DigiTorus86/ESP32Badge/hello-badge/esp32-badge-wav-play/audio_wav.h

/* D:\Projects\Assets\CodeMashBadge\alive8.wav (11/29/2019 5:37:46 PM)
   StartOffset: 00000000, EndOffset: 0000885F, Length: 00008860 
   Exported from Audacity as 8-bit 11025Hz mono PCM WAV file
   Exported from HxD Hex Editor as C code  (File -> Export -> C)
*/
   
const PROGMEM uint8_t audio_wav[34912] = {
  0x52, 0x49, 0x46, 0x46, 0x58, 0x88, 0x00, 0x00, 0x57, 0x41, 0x56, 0x45,
  0x66, 0x6D, 0x74, 0x20, 0x10, 0x00, 0x00, 0x00, 0x01, 0x00, 0x01, 0x00,
  0x11, 0x2B, 0x00, 0x00, 0x11, 0x2B, 0x00, 0x00, 0x01, 0x00, 0x08, 0x00,
  0x64, 0x61, 0x74, 0x61, 0x34, 0x88, 0x00, 0x00, 0x81, 0x80, 0x81, 0x7F,
  0x80, 0x7F, 0x7F, 0x80, 0x7F, 0x80, 0x80, 0x7F, 0x80, 0x7F, 0x80, 0x7F,
  0x80, 0x7F, 0x80, 0x7F, 0x80, 0x7F, 0x80, 0x7F, 0x80, 0x80, 0x7F, 0x80,
  0x7F, 0x80, 0x80, 0x7F, 0x80, 0x7F, 0x80, 0x80, 0x80, 0x80, 0x80, 0x7F,
  0x80, 0x80, 0x80, 0x81, 0x80, 0x7F, 0x80, 0x80, 0x7F, 0x80, 0x7F, 0x80,
  0x7F, 0x80, 0x7F, 0x80, 0x7F, 0x80, 0x7F, 0x7F, 0x80, 0x7F, 0x80, 0x7F,
  0x7F, 0x80, 0x7F, 0x80, 0x7F, 0x80, 0x7F, 0x80, 0x7F, 0x80, 0x80, 0x80,
  0x7F, 0x80, 0x7F, 0x80, 0x80, 0x7F, 0x80, 0x80, 0x7F, 0x80, 0x7F, 0x80,
  0x7F, 0x80, 0x7F, 0x80, 0x7F, 0x80, 0x80, 0x7F, 0x80, 0x7F, 0x80, 0x80,
  0x80, 0x80, 0x7F, 0x80, 0x80, 0x80, 0x80, 0x7F, 0x80, 0x7F, 0x80, 0x80,
  0x81, 0x81, 0x80, 0x81, 0x80, 0x81, 0x80, 0x80, 0x80, 0x80, 0x7F, 0x80,
  0x7F, 0x81, 0x80, 0x80, 0x80, 0x7F, 0x80, 0x7F, 0x80, 0x7F, 0x80, 0x80,
  0x81, 0x7F, 0x80, 0x80, 0x81, 0x80, 0x81, 0x7F, 0x80, 0x7F, 0x81, 0x81,
  0x80, 0x80, 0x80, 0x80, 0x81, 0x80, 0x80, 0x7F, 0x80, 0x80, 0x82, 0x80,
  0x7F, 0x81, 0x81, 0x81, 0x7F, 0x80, 0x7F, 0x80, 0x7F, 0x80, 0x7F, 0x80,
  0x7F, 0x80, 0x80, 0x80, 0x81, 0x80, 0x81, 0x80, 0x81, 0x80, 0x81, 0x81,
  0x80, 0x81, 0x80, 0x80, 0x80, 0x7F, 0x80, 0x7F, 0x80, 0x80, 0x7F, 0x80,
  0x7F, 0x80, 0x7F, 0x80, 0x81, 0x81, 0x80, 0x80, 0x81, 0x82, 0x82, 0x80,
  0x7F, 0x81, 0x81, 0x81, 0x7E, 0x7E, 0x7F, 0x80, 0x80, 0x7E, 0x7F, 0x7F,
  0x7F, 0x80, 0x80, 0x80, 0x81, 0x80, 0x81, 0x81, 0x80, 0x81, 0x80, 0x80,
  0x80, 0x80, 0x81, 0x7F, 0x7F, 0x7F, 0x7E, 0x80, 0x7F, 0x7E, 0x7F, 0x7E,
  0x80, 0x80, 0x81, 0x80, 0x81, 0x80, 0x81, 0x82, 0x82, 0x83, 0x81, 0x80,
  0x81, 0x81, 0x81, 0x80, 0x7E, 0x7F, 0x7E, 0x7F, 0x7F, 0x7E, 0x7F, 0x7F,
  0x80, 0x80, 0x81, 0x80, 0x81, 0x80, 0x82, 0x81, 0x82, 0x81, 0x81, 0x80,
  0x81, 0x81, 0x7F, 0x7F, 0x7F, 0x7E, 0x7F, 0x7F, 0x7F, 0x7E, 0x7F, 0x7F,
  0x80, 0x81, 0x80, 0x81, 0x81, 0x82, 0x81, 0x82, 0x80, 0x80, 0x7F, 0x81,
  0x82, 0x85, 0x84, 0x7E, 0x7B, 0x7E, 0x82, 0x84, 0x7D, 0x79, 0x78, 0x7E,
  0x82, 0x84, 0x7F, 0x7D, 0x7F, 0x83, 0x85, 0x86, 0x83, 0x81, 0x80, 0x81,
  0x85, 0x84, 0x82, 0x7D, 0x7D, 0x7E, 0x81, 0x80, 0x7D, 0x7A, 0x7B, 0x7E,
  0x81, 0x80, 0x7E, 0x7F, 0x80, 0x83, 0x82, 0x83, 0x82, 0x82, 0x82, 0x81,
  0x82, 0x7F, 0x7E, 0x7E, 0x7F, 0x84, 0x84, 0x7E, 0x7B, 0x7C, 0x81, 0x83,
  0x82, 0x7E, 0x7C, 0x7F, 0x83, 0x83, 0x82, 0x80, 0x7E, 0x81, 0x82, 0x84,
  0x81, 0x80, 0x7E, 0x80, 0x82, 0x82, 0x81, 0x7F, 0x7E, 0x7F, 0x80, 0x81,
  0x7F, 0x7F, 0x7F, 0x7E, 0x7E, 0x80, 0x7F, 0x80, 0x7E, 0x7E, 0x80, 0x80,
  0x81, 0x80, 0x80, 0x80, 0x80, 0x7F, 0x7F, 0x80, 0x88, 0x8B, 0x82, 0x78,
  0x79, 0x80, 0x87, 0x80, 0x77, 0x74, 0x7A, 0x85, 0x84, 0x80, 0x7C, 0x7F,
  0x83, 0x88, 0x87, 0x85, 0x81, 0x7F, 0x82, 0x84, 0x86, 0x82, 0x7D, 0x79,
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
};
