DigiTorus86/ESP32Badge/esp32-badge-gravitack/TickWav.h

/* D:\Projects\Assets\CodeMashBadge\tickGx8.wav (9/9/2019 5:25:52 PM)
   StartOffset: 00000000, EndOffset: 000005E5, Length: 000005E6 */

unsigned char tick_wav[1510] = {
  0x52, 0x49, 0x46, 0x46, 0xDE, 0x05, 0x00, 0x00, 0x57, 0x41, 0x56, 0x45,
  0x66, 0x6D, 0x74, 0x20, 0x10, 0x00, 0x00, 0x00, 0x01, 0x00, 0x01, 0x00,
  0x22, 0x56, 0x00, 0x00, 0x22, 0x56, 0x00, 0x00, 0x01, 0x00, 0x08, 0x00,
  0x64, 0x61, 0x74, 0x61, 0xBA, 0x05, 0x00, 0x00, 0x7E, 0x7F, 0x82, 0x82,
  0x7E, 0x7E, 0x82, 0x83, 0x7E, 0x7B, 0x80, 0x83, 0x7D, 0x78, 0x8B, 0xB5,
  0xDF, 0xF7, 0xFF, 0xF8, 0xCE, 0x80, 0x30, 0x05, 0x00, 0x00, 0x01, 0x27,
  0x7A, 0xCF, 0xFC, 0xFF, 0xFD, 0xE6, 0xA9, 0x52, 0x13, 0x00, 0x00, 0x00,
  0x15, 0x58, 0xB0, 0xEC, 0xFF, 0xFF, 0xF5, 0xC6, 0x74, 0x29, 0x06, 0x01,
  0x00, 0x0C, 0x41, 0x94, 0xDA, 0xF9, 0xFF, 0xFA, 0xDA, 0x97, 0x48, 0x15,
  0x03, 0x00, 0x06, 0x2C, 0x73, 0xBD, 0xEC, 0xFF, 0xFF, 0xE9, 0xB2, 0x68,
  0x2B, 0x0B, 0x00, 0x02, 0x1C, 0x57, 0xA0, 0xDA, 0xF8, 0xFF, 0xF2, 0xC9,
  0x89, 0x47, 0x19, 0x04, 0x01, 0x14, 0x41, 0x83, 0xC2, 0xEC, 0xFD, 0xF8,
  0xD9, 0xA2, 0x62, 0x2D, 0x0E, 0x04, 0x0E, 0x30, 0x69, 0xA9, 0xDB, 0xF6,
  0xF9, 0xE5, 0xB9, 0x7E, 0x44, 0x1B, 0x09, 0x0B, 0x23, 0x52, 0x8E, 0xC6,
  0xEB, 0xF8, 0xED, 0xCB, 0x97, 0x5E, 0x2F, 0x12, 0x0B, 0x1B, 0x40, 0x76,
  0xAD, 0xDA, 0xF1, 0xF1, 0xD9, 0xAD, 0x77, 0x45, 0x20, 0x10, 0x17, 0x33,
  0x61, 0x96, 0xC6, 0xE7, 0xF1, 0xE2, 0xBE, 0x8E, 0x5C, 0x33, 0x1B, 0x17,
  0x29, 0x4E, 0x7F, 0xB1, 0xD7, 0xEA, 0xE6, 0xCD, 0xA3, 0x73, 0x46, 0x27,
  0x1B, 0x24, 0x40, 0x6A, 0x9A, 0xC5, 0xE0, 0xE6, 0xD6, 0xB4, 0x87, 0x5A,
  0x37, 0x23, 0x23, 0x36, 0x59, 0x86, 0xB1, 0xD2, 0xE0, 0xDA, 0xC1, 0x9A,
  0x6F, 0x48, 0x2E, 0x25, 0x30, 0x4B, 0x73, 0x9D, 0xC2, 0xD9, 0xDC, 0xCB,
  0xAA, 0x82, 0x5A, 0x3B, 0x2B, 0x2D, 0x41, 0x62, 0x8A, 0xB1, 0xCC, 0xD8,
  0xD0, 0xB8, 0x94, 0x6C, 0x4A, 0x34, 0x2E, 0x3A, 0x54, 0x78, 0x9F, 0xBF,
  0xD1, 0xD1, 0xC0, 0xA2, 0x7E, 0x5B, 0x40, 0x33, 0x36, 0x4A, 0x69, 0x8D,
  0xAF, 0xC7, 0xCF, 0xC7, 0xAF, 0x8F, 0x6B, 0x4D, 0x3A, 0x36, 0x43, 0x5C,
  0x7D, 0x9F, 0xBB, 0xCA, 0xC9, 0xB9, 0x9D, 0x7B, 0x5C, 0x44, 0x3A, 0x3E,
  0x51, 0x6D, 0x8E, 0xAD, 0xC1, 0xC7, 0xBE, 0xA8, 0x8A, 0x6B, 0x50, 0x40,
  0x3E, 0x4A, 0x61, 0x7F, 0x9E, 0xB6, 0xC3, 0xC1, 0xB2, 0x98, 0x7A, 0x5E,
  0x49, 0x41, 0x46, 0x56, 0x70, 0x8E, 0xA9, 0xBB, 0xC0, 0xB7, 0xA3, 0x88,
  0x6C, 0x54, 0x46, 0x45, 0x4F, 0x65, 0x80, 0x9B, 0xB1, 0xBC, 0xBA, 0xAD,
  0x96, 0x7A, 0x61, 0x4F, 0x47, 0x4B, 0x5A, 0x72, 0x8D, 0xA5, 0xB5, 0xBA,
  0xB2, 0xA1, 0x88, 0x6F, 0x59, 0x4C, 0x4A, 0x53, 0x66, 0x7E, 0x97, 0xAB,
  0xB5, 0xB5, 0xA9, 0x95, 0x7D, 0x66, 0x54, 0x4C, 0x4F, 0x5C, 0x71, 0x89,
  0x9F, 0xAE, 0xB4, 0xAE, 0xA0, 0x8B, 0x74, 0x60, 0x52, 0x4F, 0x55, 0x65,
  0x7A, 0x90, 0xA3, 0xAF, 0xB1, 0xA9, 0x98, 0x83, 0x6D, 0x5C, 0x52, 0x52,
  0x5C, 0x6C, 0x81, 0x95, 0xA6, 0xAE, 0xAD, 0xA2, 0x91, 0x7C, 0x69, 0x5A,
  0x54, 0x56, 0x60, 0x71, 0x85, 0x98, 0xA6, 0xAC, 0xA9, 0x9E, 0x8D, 0x79,
  0x67, 0x5B, 0x56, 0x59, 0x63, 0x74, 0x87, 0x98, 0xA5, 0xAA, 0xA6, 0x9C,
  0x8C, 0x7A, 0x69, 0x5D, 0x57, 0x5A, 0x64, 0x73, 0x85, 0x95, 0xA2, 0xA7,
  0xA5, 0x9C, 0x8E, 0x7D, 0x6D, 0x61, 0x5A, 0x5B, 0x62, 0x6F, 0x7F, 0x8F,
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
};
