DigiTorus86/ESP32Badge/esp32-badge-tombstone/Audio.h

/*
 * Audio and sound
 */


//Fifth Octave Note Frequencies
 
#define C5 523 // C note frequency
#define Cs5 554 // C sharp note frequency (same as D flat)
#define D5 587 // D note frequency
#define Ds5 622 // D sharp note frequency (same as E flat)
#define E5 659 // E note frequency
#define F5 698 // F note frequency
#define Fs5 740 // F sharp note frequency (same as G flat)
#define G5 784 // G note frequency
#define Gs5 831 // G sharp note frequency (same as A flat)
#define A5 880 // A note frequency
#define As5 932 // A sharp note frequency (same as B flat)
#define B5 988 // B note frequency
 
//Sixth Octave Note Frequencies
 
#define C6 1046 // note frequency
#define Cs6 1109 // sharp note frequency ( same as D flat)
#define D6 1175 // note frequency
#define Ds6 1245 // sharp note frequency ( same as E flat)
#define E6 1319 // note frequency
#define F6 1397 // note frequency
#define Fs6 1480 // sharp note frequency (same as G flat)
#define G6 1568 // note frequency
#define Gs6 1661 // sharp note frequency (same as A flat)
#define A6 1760 // note frequency
#define As6 1865 // sharp note frequency ( same as B flat)
#define B6 1976 // note frequency

#define QTR_NOTE   300
#define HALF_NOTE  600
#define WHOLE_NOTE 900
